go4retro/HEXTIr/pcb/Fritzing/HexBusSDUno_bb.png

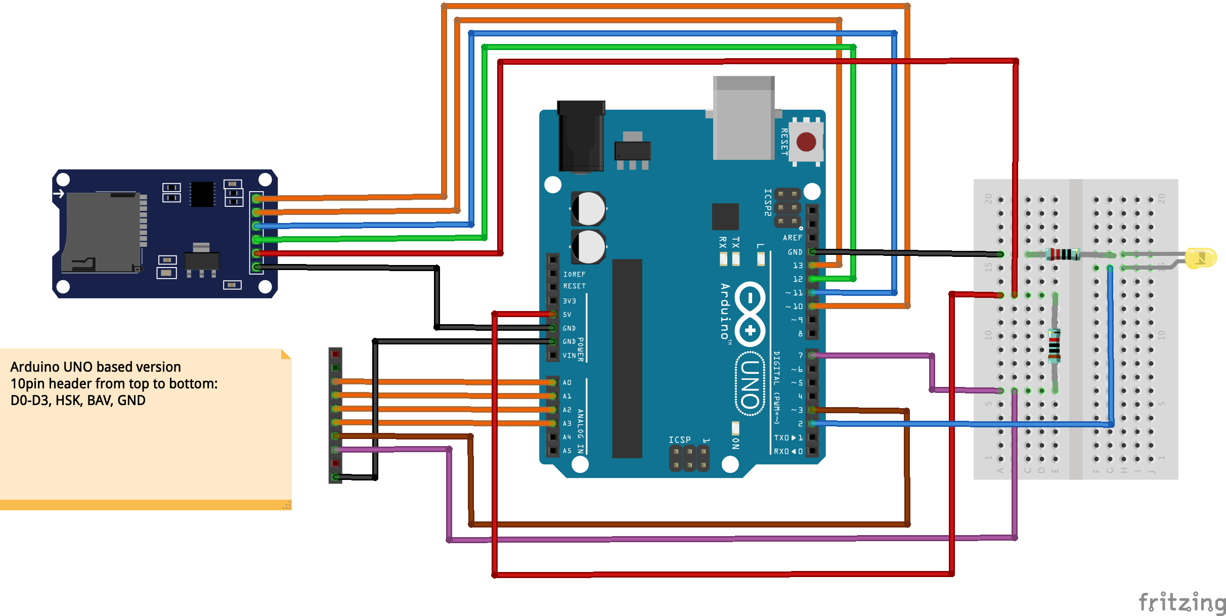
pcb/Fritzing/HexBusSDUno_bb.png
