go4retro/HEXTIr/src/pcf8583.cpp

/*
    HEXTIr-SD - Texas Instruments HEX-BUS SD Mass Storage Device
    Copyright Jim Brain and RETRO Innovations, 2017

    This code is a modification of the file from the following project:

    sd2iec - SD/MMC to Commodore serial bus interface/controller
    Copyright (C) 2007-2017  Ingo Korb <ingo@akana.de>

    Inspired by MMC2IEC by Lars Pontoppidan et al.

    FAT filesystem access based on code from ChaN and Jim Brain, see ff.c|h.

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
    pcf8583.c: RTC support for PCF8583 chips

    The exported functions in this file are weak-aliased to their corresponding
    versions defined in rtc.h so when this file is the only RTC implementation
    compiled in they will be automatically used by the linker.

*/

#include <stdint.h>
#include <string.h>
#include <avr/pgmspace.h>

#include "config.h"
#include "debug.h"
#include "i2c.h"
#include "time.h"
#include "rtc.h"
#include "pcf8583.h"

#ifdef CONFIG_RTC_PCF8583   // hide file from Arduino if not enabled

#if defined(I2C_EEPROM_ADDRESS) && I2C_EEPROM_ADDRESS == 0xa0
#  define PCF8583_ADDR 0xa2
#else
#  define PCF8583_ADDR 0xa0
#endif

#define REG_CONTROL 0
#define REG_S100    1
#define REG_SECONDS 2
#define REG_MINUTES 3
#define REG_HOURS   4
#define REG_YDATE   5
#define REG_WMONTH  6
/* Use the first four ram bytes to store the year and its complement.       */
/* If the complement doesn't match the RTC contents are considered invalid. */
#define REG_YEAR1   16
#define REG_YEAR2   17
#define REG_YEARC1  18
#define REG_YEARC2  19

#define CTL_STOP_CLOCK  0x80
#define CTL_START_CLOCK 0

/* Read the current time from the RTC */
/* Will auto-adjust the stored year if required */
void pcf8583_get(struct tm *time) {
  union {
    uint8_t  bytes[5];
    uint16_t words[2];
  } tmp;

  /* Set to default value in case we abort */
  memcpy_P(time, &rtc_default_date, sizeof(struct tm));
  if (rtc_state != RTC_OK)
    return;

  if (i2c_read_registers(PCF8583_ADDR, REG_SECONDS, 5, &tmp))
    return;

  time->tm_sec  = bcd2int(tmp.bytes[0]);
  time->tm_min  = bcd2int(tmp.bytes[1]);
  time->tm_hour = bcd2int(tmp.bytes[2]);
  time->tm_mday = bcd2int(tmp.bytes[3] & 0b00111111);
  time->tm_mon  = bcd2int(tmp.bytes[4] & 0b00011111)-1;
  time->tm_wday = bcd2int(tmp.bytes[4] >> 5);

  /* Check for year rollover */
  tmp.bytes[4] = tmp.bytes[3] >> 6;
  i2c_read_registers(PCF8583_ADDR, REG_YEAR1, 4, &tmp);
  if ((tmp.words[0] & 3) != tmp.bytes[4]) {
    /* Year rolled over, increment until the lower two bits match */
    while ((tmp.words[0] & 3) != tmp.bytes[4]) tmp.words[0]++;
    tmp.words[1] = tmp.words[0] ^ 0xffffU;

    /* Store new year to RTC ram */
    i2c_write_registers(PCF8583_ADDR, REG_YEAR1, 4, &tmp);
  }

  time->tm_year = tmp.words[0]-1900;
}
void rtc_get(struct tm *time) __attribute__ ((weak, alias("pcf8583_get")));

/* Set the time in the RTC */
void pcf8583_set(struct tm *time) {
  union {
    uint8_t  bytes[5];
    uint16_t words[2];
  } tmp;

  if (rtc_state == RTC_NOT_FOUND)
    return;

  i2c_write_register(PCF8583_ADDR, REG_CONTROL, CTL_STOP_CLOCK);
  tmp.bytes[0] = int2bcd(time->tm_sec);
  tmp.bytes[1] = int2bcd(time->tm_min);
  tmp.bytes[2] = int2bcd(time->tm_hour);
  tmp.bytes[3] = int2bcd(time->tm_mday) | ((time->tm_year & 3) << 6);
  tmp.bytes[4] = int2bcd(time->tm_mon+1)| ((time->tm_wday    ) << 5);
  i2c_write_registers(PCF8583_ADDR, REG_SECONDS, 5, &tmp);
  tmp.words[0] = time->tm_year + 1900;
  tmp.words[1] = (time->tm_year + 1900) ^ 0xffffU;
  i2c_write_registers(PCF8583_ADDR, REG_YEAR1, 4, &tmp);
  i2c_write_register(PCF8583_ADDR, REG_CONTROL, CTL_START_CLOCK);
  rtc_state = RTC_OK;
}
void rtc_set(struct tm *time) __attribute__ ((weak, alias("pcf8583_set")));

rtc_type_t pcf8583_get_type(void) {
  return RTC_TYPE_HW;
}
rtc_type_t rtc_get_type(void) __attribute__ ((weak, alias("pcf8583_get_type")));

void pcf8583_init(void) {
  uint8_t tmp[4];

  i2c_init();
  rtc_state = RTC_NOT_FOUND;
  debug_puts_P("PCF8583 ");
  if (i2c_write_register(PCF8583_ADDR, REG_CONTROL, CTL_START_CLOCK) ||
      i2c_read_registers(PCF8583_ADDR, REG_YEAR1, 4, tmp)) {
    debug_puts_P("not found");
  } else {
    if (tmp[0] == (tmp[2] ^ 0xff) &&
        tmp[1] == (tmp[3] ^ 0xff)) {
      rtc_state = RTC_OK;
      debug_puts_P("ok");

      /* Dummy RTC read to update the year if required */
      struct tm time;
      rtc_get(&time);
    } else {
      rtc_state = RTC_INVALID;
      debug_puts_P("invalid");
    }
  }

  debug_putcrlf();
}
void rtc_init(void) __attribute__ ((weak, alias("pcf8583_init")));
#endif
