go4retro/HEXTIr/src/hexbus.h

/*
    HEXTIr-SD - Texas Instruments HEX-BUS SD Mass Storage Device
    Copyright Jim Brain and RETRO Innovations, 2017

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
    hexbus.h: TI Hex Bus definitions and low level functions
*/

#ifndef SRC_HEXBUS_H_
#define SRC_HEXBUS_H_
#ifdef __cplusplus
extern "C"{
#endif

#include "integer.h"

#define DEV_NONE      0
#define DEV_ALL       DEV_NONE  // Device Code 0 addresses all devices
#define DEV_MAX       255       // our highest device code

typedef enum _hexcmdtype_t {
               HEXCMD_OPEN = 0,
               HEXCMD_CLOSE,
               HEXCMD_DELETE_OPEN,
               HEXCMD_READ,
               HEXCMD_WRITE,
               HEXCMD_RESTORE,
               HEXCMD_DELETE,
               HEXCMD_RETURN_STATUS,
               HEXCMD_SVC_REQ_ENABLE,
               HEXCMD_SVC_REQ_DISABLE,
               HEXCMD_SVC_REQ_POLL,
               HEXCMD_MASTER,
               HEXCMD_VERIFY,
               HEXCMD_FORMAT,
               HEXCMD_CATALOG,
               HEXCMD_SET_OPTIONS,
               HEXCMD_XMIT_BREAK,
               HEXCMD_WP_FILE,
               HEXCMD_READ_SECTORS,
               HEXCMD_WRITE_SECTORS,
               HEXCMD_RENAME_FILE,
               HEXCMD_READ_FD,
               HEXCMD_WRITE_FD,
               HEXCMD_READ_FILE_SECTORS,
               HEXCMD_WRITE_FILE_SECTORS,
               HEXCMD_LOAD,
               HEXCMD_SAVE,
               HEXCMD_INQ_SAVE,
               HEXCMD_HOME_COMP_STATUS,
               HEXCMD_HOME_COMP_VERIFY,
               HEXCMD_NULL = 0xfe,
               HEXCMD_RESET_BUS
            } hexcmdtype_t;

typedef enum _hexstatus_t {
              HEXSTAT_SUCCESS = 0,
              HEXSTAT_OPTION_ERR,
              HEXSTAT_ATTR_ERR,
              HEXSTAT_NOT_FOUND,
              HEXSTAT_NOT_OPEN,
              HEXSTAT_ALREADY_OPEN,
              HEXSTAT_DEVICE_ERR,
              HEXSTAT_EOF,
              HEXSTAT_TOO_LONG,
              HEXSTAT_WP_ERR,
              HEXSTAT_NOT_REQUEST,
              HEXSTAT_DIR_FULL,
              HEXSTAT_BUF_SIZE_ERR,
              HEXSTAT_UNSUPP_CMD,
              HEXSTAT_NOT_WRITE,
              HEXSTAT_NOT_READ,
              HEXSTAT_DATA_ERR,
              HEXSTAT_FILE_TYPE_ERR,
              HEXSTAT_FILE_PROT_ERR,
              HEXSTAT_APPEND_MODE_ERR,
              HEXSTAT_OUTPUT_MODE_ERR,
              HEXSTAT_INPUT_MODE_ERR,
              HEXSTAT_UPDATE_MODE_ERR,
              HEXSTAT_FILE_TYPE_INT_DISP_ERR,
              HEXSTAT_VERIFY_ERR,
              HEXSTAT_BATT_LOW,
              HEXSTAT_UNFORMATTED,
              HEXSTAT_BUS_ERR,
              HEXSTAT_DEL_PROTECT,
              HEXSTAT_CART_NOT_PRESENT,
              HEXSTAT_RESTORE_NOT_ALLOWED,
              HEXSTAT_FILE_NAME_INVALID,
              HEXSTAT_MEDIA_FULL,
              HEXSTAT_MAX_LUNS,
              HEXSTAT_DATA_INVALID,
              HEXSTAT_ILLEGAL_SLAVE = 0xfe,
              HEXSTAT_TIMEOUT
            } hexstatus_t;

typedef enum _hexerror_t {
              HEXERR_SUCCESS = 0,
              HEXERR_BAV = -1,
              HEXERR_TIMEOUT = -2
            } hexerror_t;

typedef enum _openmode_t {
              OPENMODE_UPDATE =     0xC0, // update mode is read AND write
              OPENMODE_READ =       0x40, // input only
              OPENMODE_WRITE =      0x80, // output only
              OPENMODE_APPEND =     0x00, // append mode is specified by read and write both = 0.
              OPENMODE_RELATIVE =   0x20, // relative is used for records, often associated with fixed
              OPENMODE_FIXED =      0x10, // fixed says each file has fixed length 'records'
              OPENMODE_INTERNAL =   0x08, // internal type files store data in native form rather than ASCII (ie. numbers are stored in internal format.
            } openmode_t ;

#define OPENMODE_MASK               (OPENMODE_READ | OPENMODE_WRITE)


#define    FILE_EOF_REACHED         0x80
#define    FILE_SUPPORTS_RELATIVE   0x40
#define    FILE_IS_PROTECTED        0x20
#define    FILE_DEV_IS_OPEN         0x10
#define    FILE_DEV_TYPE_MASK       0x0C
#define    FILE_DEV_TYPE_DATACOM    0x08
#define    FILE_DEV_TYPE_INTERNAL   0x04
#define    FILE_DEV_TYPE_DISPLAY    0x00
#define    FILE_IO_MODE_MASK        0x03
#define    FILE_IO_MODE_READWRITE   0x03
#define    FILE_IO_MODE_WRITEONLY   0x02
#define    FILE_IO_MODE_READONLY    0x01
#define    FILE_REQ_STATUS_NONE     0x00


uint8_t hex_is_bav(void);
void hex_release_bus(void);
hexerror_t hex_capture_hsk( void );
hexerror_t hex_recv_byte( uint8_t *inout);
hexerror_t hex_send_byte( uint8_t xmit );
hexerror_t hex_send_word( uint16_t value );
void hex_finish( void );
void hex_send_size_response( uint16_t len , uint16_t record);
void hex_send_final_response( hexstatus_t rc );
void hex_init(void);

#ifdef __cplusplus
} // extern "C"
#endif

#endif /* SRC_HEXBUS_H_ */
