go4retro/HEXTIr/src/diskio.cpp

/*
    HEXTIr-SD - Texas Instruments HEX-BUS SD Mass Storage Device
    Copyright Jim Brain and RETRO Innovations, 2017

    This code is a modification of the file from the following project:

    sd2iec - SD/MMC to Commodore serial bus interface/controller
    Copyright (C) 2007-2017  Ingo Korb <ingo@akana.de>

    Inspired by MMC2IEC by Lars Pontoppidan et al.

    FAT filesystem access based on code from ChaN and Jim Brain, see ff.c|h.

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
   diskio.c: Generic disk access routines and supporting stuff

*/

#include "config.h"
#include "diskio.h"
#include "sdcard.h"

volatile enum diskstates disk_state;

#ifdef NEED_DISKMUX

uint32_t drive_config;

/* This function calculates the default drive configuration. */
/* Its result is static after compilation, but doing this in */
/* C in less messy than doing it with the preprocessor.      */
uint32_t get_default_driveconfig(void) {
  uint32_t result = 0xffffffffL;

  /* Order matters: Whatever is checked first will be last in the config */
#ifdef CONFIG_TWINSD
  result = (result << 4) + (DISK_TYPE_SD  << DRIVE_BITS) + 1;
#endif
#ifdef HAVE_SD
  result = (result << 4) + (DISK_TYPE_SD  << DRIVE_BITS) + 0;
#endif
#ifdef HAVE_ATA
  result = (result << 4) + (DISK_TYPE_ATA << DRIVE_BITS) + 0;
#endif
  return result;
}

void disk_init(void) {
#ifdef HAVE_SD
  sd_init();
#endif
#ifdef HAVE_ATA
  ata_init();
#endif
}

DSTATUS disk_status(BYTE drv) {
  switch(drv >> DRIVE_BITS) {
#ifdef HAVE_ATA
  case DISK_TYPE_ATA:
    return ata_status(drv & DRIVE_MASK);

  case DISK_TYPE_ATA2:
    return ata_status((drv & DRIVE_MASK) + 2);
#endif

#ifdef HAVE_SD
  case DISK_TYPE_SD:
    return sd_status(drv & DRIVE_MASK);
#endif

  default:
    return STA_NOINIT|STA_NODISK;
  }
}

DSTATUS disk_initialize(BYTE drv) {
  switch(drv >> DRIVE_BITS) {
#ifdef HAVE_ATA
  case DISK_TYPE_ATA:
    return ata_initialize(drv & DRIVE_MASK);

  case DISK_TYPE_ATA2:
    return ata_initialize((drv & DRIVE_MASK) + 2);
#endif

#ifdef HAVE_SD
  case DISK_TYPE_SD:
    return sd_initialize(drv & DRIVE_MASK);
#endif

  default:
    return STA_NOINIT|STA_NODISK;
  }
}

DRESULT disk_read(BYTE drv, BYTE *buffer, DWORD sector, BYTE count) {
  switch(drv >> DRIVE_BITS) {
#ifdef HAVE_ATA
  case DISK_TYPE_ATA:
    return ata_read(drv & DRIVE_MASK,buffer,sector,count);

  case DISK_TYPE_ATA2:
    return ata_read((drv & DRIVE_MASK) + 2,buffer,sector,count);
#endif

#ifdef HAVE_SD
  case DISK_TYPE_SD:
    return sd_read(drv & DRIVE_MASK,buffer,sector,count);
#endif

  default:
    return RES_ERROR;
  }
}

DRESULT disk_write(BYTE drv, const BYTE *buffer, DWORD sector, BYTE count) {
  switch(drv >> DRIVE_BITS) {
#ifdef HAVE_ATA
  case DISK_TYPE_ATA:
    return ata_write(drv & DRIVE_MASK,buffer,sector,count);

  case DISK_TYPE_ATA2:
    return ata_write((drv & DRIVE_MASK) + 2,buffer,sector,count);
#endif

#ifdef HAVE_SD
  case DISK_TYPE_SD:
    return sd_write(drv & DRIVE_MASK,buffer,sector,count);
#endif

  default:
    return RES_ERROR;
  }
}

DRESULT disk_getinfo(BYTE drv, BYTE page, void *buffer) {
  switch(drv >> DRIVE_BITS) {
#ifdef HAVE_ATA
  case DISK_TYPE_ATA:
    return ata_getinfo(drv & DRIVE_MASK,page,buffer);

  case DISK_TYPE_ATA2:
    return ata_getinfo((drv & DRIVE_MASK) + 2,page,buffer);
#endif

#ifdef HAVE_SD
  case DISK_TYPE_SD:
    return sd_getinfo(drv & DRIVE_MASK,page,buffer);
#endif

  default:
    return RES_ERROR;
  }
}


#endif
