go4retro/HEXTIr/src/eeprom.c

/*
    HEXTIr-SD - Texas Instruments HEX-BUS SD Mass Storage Device
    Copyright Jim Brain and RETRO Innovations, 2017

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
    eeprom.c: Configuration storage
*/

#include <stddef.h>
#include <string.h>
#include <avr/eeprom.h>
#include "config.h"
#include "debug.h"
#include "integer.h"
#include "eeprom.h"

static EEMEM config_t _eeconfig;

config_t _config;

/**
 * ee_get_config - reads configuration from EEPROM
 *
 * This function reads the stored configuration values from the EEPROM.
 * If the stored checksum doesn't match the calculated one defaults
 * will be returned
 */
void ee_get_config(void) {
  uint_fast16_t i, size;
  uint8_t checksum;

  /* Set default values */

  /* done setting defaults */

  size = eeprom_read_word(&_eeconfig.structsize);

  /* Calculate checksum of EEPROM contents */
  checksum = 0;
  for (i = 2; i < size; i++)
    checksum += eeprom_read_byte((uint8_t *)(&_eeconfig) + i);

  /* Abort if the checksum doesn't match */
  if (checksum != eeprom_read_byte(&_eeconfig.checksum)) {
    eeprom_safety();
    _config.valid = FALSE;
  } else {
    /* Read data from EEPROM */
    eeprom_read_block(&_config, &_eeconfig, size);
    _config.valid = TRUE;
  }
  /* Prevent problems due to accidental writes */
  eeprom_safety();
}

/**
 * ee_set_config - stores configuration data to EEPROM
 *
 * This function stores the current configuration values to the EEPROM.
 */
void ee_set_config(void) {
  uint_fast16_t i;
  uint8_t checksum;

  /* Calculate checksum over EEPROM contents */
  checksum = 0;
  for (i = 2; i < sizeof(config_t); i++)
    checksum += *((uint8_t *) &_config + i);
  /* Write configuration to EEPROM */
  _config.structsize = sizeof(config_t);
  _config.checksum = checksum;
  eeprom_write_block(&_config, &_eeconfig, _config.structsize);
  //debug_trace(&_config,0,sizeof(config_t));

  /* Prevent problems due to accidental writes */
  eeprom_safety();
}
