go4retro/HEXTIr/src/eeprom.h

/* sd2iec - SD/MMC to Commodore serial bus interface/controller
   Copyright (C) 2007-2011  Ingo Korb <ingo@akana.de>

   Inspiration and low-level SD/MMC access based on code from MMC2IEC
     by Lars Pontoppidan et al., see sdcard.c|h and config.h.

   FAT filesystem access based on code from ChaN and Jim Brain, see ff.c|h.

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

   eeprom.h: Persistent configuration storage

*/

#ifndef EEPROM_H
#define EEPROM_H
#include "config.h"
#ifdef INCLUDE_CLOCK
#include "clock.h"
#endif
#ifdef INCLUDE_SERIAL
#include "serial.h"
#endif
#ifdef INCLUDE_PRINTER
#include "printer.h"
#endif
#ifdef __cplusplus
extern "C"{
#endif

/**
 * struct config_s - in-eeprom data structure
 * @dummy      : EEPROM position 0 is unused
 * @checksum   : Checksum over the EEPROM contents
 * @structsize : size of the eeprom structure
 * @glob_flags : global flags
 * @device structures
 *
 * This is the data structure for the contents of the EEPROM.
 *
 * Do not remove any fields!
 * Only add fields at the end!
 */
typedef struct config_s {
  uint8_t     valid;
  uint8_t     checksum;
  uint16_t    structsize;
  uint8_t     glob_flags;
// drive section
#ifdef INCLUDE_DRIVE
  uint8_t     drv_dev;
#endif
#ifdef INCLUDE_CLOCK
  uint8_t     clk_dev;
#endif
#ifdef INCLUDE_SERIAL
  uint8_t     ser_dev;
  serialcfg_t ser;
#endif
#ifdef INCLUDE_PRINTER
  uint8_t     prn_dev;
  printcfg_t  prn;
#endif
} config_t;

extern config_t _config;

/* Set EEPROM address pointer to the dummy entry */
static inline void eeprom_safety(void) {
  EEAR = 0;
}

void ee_get_config(void);
void ee_set_config(void);

#ifdef __cplusplus
} // extern "C"
#endif
#endif
